zhyma/force_sensing_handbrake/img/top_view.jpg

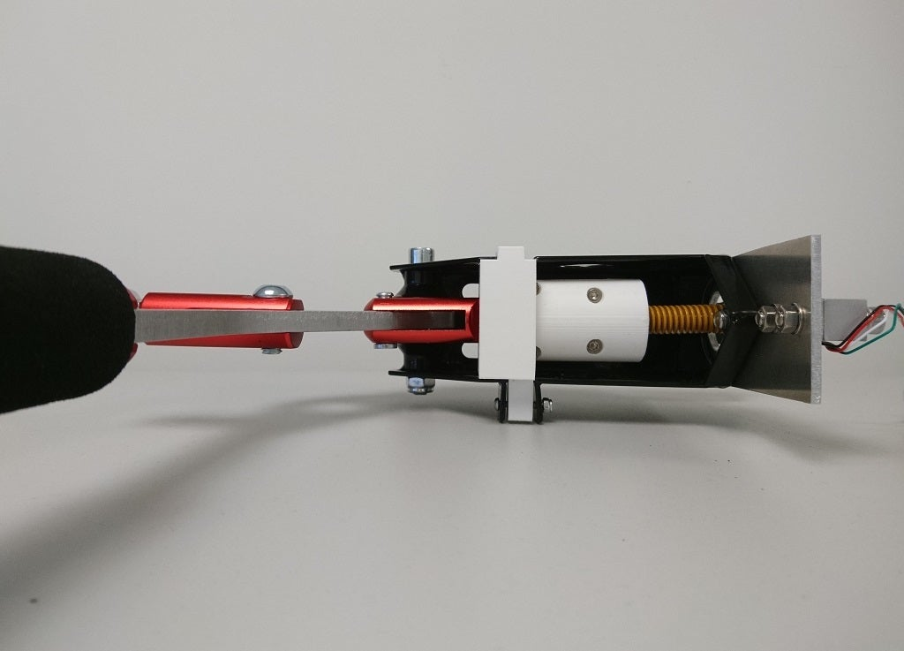
img/top_view.jpg
